karmakrafts/EtherKraken/etherkraken-bootloader2/src/main.c

// Copyright 2026 Karma Krafts
//
// Licensed under the Apache License, Version 2.0 (the "License");
// you may not use this file except in compliance with the License.
// You may obtain a copy of the License at
//
// http://www.apache.org/licenses/LICENSE-2.0
//
// Unless required by applicable law or agreed to in writing, software
// distributed under the License is distributed on an "AS IS" BASIS,
// WITHOUT WARRANTIES OR CONDITIONS OF ANY KIND, either express or implied.
// See the License for the specific language governing permissions and
// limitations under the License.

/**
 * bootloader2 is started to stream firmware updates into memory
 * and flash them persistently to the coprocessors internal flash.
 * It performs the following actions when started:
 *
 * - Configure UART interface (with HFC)
 * - Send acknowledgement to main processor via UART
 * - Wait for main processor to respond with boot command
 *  -> 0x00: boot from internal flash (soft reset system)
 *      soft reset coprocessor
 *  -> 0x01: receive firmware and store in RAM
 *      receive length prefixed binary blob via UART
 *  -> 0x02: boot from RAM
 *      jump to the start address of the received binary blob
 *  -> 0x03: flash firmware stored in RAM to internal flash
 *      copy the received binary blob to the internal flash
 */

#include "bl2_cpu.h"
#include "bl2_uart.h"

int main() {
    bl2_uart_init();// We take over the UART from the ROM bootloader
    while(true) {
        // TODO: handle UART commands from main processor
        bl2_wfi();// Wait for next interrupt
    }
}
